baldufal/hpctl_avr/HPCtl/twislave.c

/*
* twislave.c
*
* Created: 23-Dec-22
* Author : Falk
* Source: https://rn-wissen.de/wiki/index.php/TWI_Slave_mit_avr-gcc
*
* We support all three types of I2C transactions:
* - Pure write: One byte can be written to address 0x0 to 0x3
* - Pure read: 6 bytes can be read, starting from address 0x0
* - Write+read: This is actually just a read from some given address (the one byte written).
*/

#include <util/twi.h>
#include <avr/interrupt.h>
#include <stdint.h>
#include "twislave.h"

// The currently selected register address (within i2cdata) to be read from/written to.
volatile uint8_t buffer_addr;

void init_twi_slave(uint8_t addr) {
	// I2C addresses are 7 bits! We have to shift.
	TWAR = (addr << 1);
	TWCR &= ~((1 << TWSTA) | (1 << TWSTO));
	TWCR |= (1 << TWEA) | (1 << TWEN) | (1 << TWIE);
	buffer_addr = 0xFF;
}

// Macros for TWI control register bitmasks

// ACK nach empfangenen Daten senden/ ACK nach gesendeten Daten erwarten
#define TWCR_ACK TWCR = (1<<TWEN)|(1<<TWIE)|(1<<TWINT)|(1<<TWEA)|(0<<TWSTA)|(0<<TWSTO)|(0<<TWWC);

// NACK nach empfangenen Daten senden/ NACK nach gesendeten Daten erwarten
#define TWCR_NACK TWCR = (1<<TWEN)|(1<<TWIE)|(1<<TWINT)|(0<<TWEA)|(0<<TWSTA)|(0<<TWSTO)|(0<<TWWC);

// Switch to the non-addressed slave mode...
#define TWCR_RESET TWCR = (1<<TWEN)|(1<<TWIE)|(1<<TWINT)|(1<<TWEA)|(0<<TWSTA)|(1<<TWSTO)|(0<<TWWC); buffer_addr=0xFF;

// TWI interrupt service routine
ISR (TWI_vect) {
	uint8_t data = 0;

	// Check TWI status register
	switch (TW_STATUS) {
		/*
		* Slave Receiver
		*/

		// 0x60 SLA+W received, ACK returned
		case TW_SR_SLA_ACK:
		// Receive next byte of data, send ACK afterwards
		TWCR_ACK;
		// Set "register address" to undefined
		buffer_addr = 0xFF;
		break;

		// 0x80 data received, ACK returned
		case TW_SR_DATA_ACK:
		// Read received data
		data = TWDR;

		// First access of this transaction, set register address
		if (buffer_addr == 0xFF) {
			// First byte of this transaction
			// This specifies the register address, usually.
			if (data < i2c_buffer_size) {
				buffer_addr = data;
			}

			// Receive next byte, ACK afterwards to request next byte
			TWCR_ACK;
			} else {
			// Subsequent byte(s) of this transaction
			// We can now receive data and use it.

			// Check which address we write to
			switch(buffer_addr) {
				// Temporary inconsistency of status register is fine because interrupts are disabled.
				
				case 0:
				// Heater Level
				if(data <= 30)
				i2cdata[buffer_addr] = data;
				break;
				
				case 1:
				// Vent IN
				if(data <= 6)
				i2cdata[buffer_addr] = data;
				break;
				
				case 2:
				// Vent OUT
				i2cdata[buffer_addr] = data;
				break;
				
				case 3:
				// SSRs
				
				// Some bits are write protected because they are set by heater level and ventilator PWM.
				i2cdata[buffer_addr] &= 0b11101000;
				i2cdata[buffer_addr] |= (data & 0b00010111);
				break;
				
				// Ignore writes to other addresses
			}

			// Increase address for subsequent writes
			buffer_addr++;

			// Receive next byte, ACK afterwards to request next byte
			TWCR_ACK;
		}
		break;

		// 0xA0 stop or repeated start condition received while selected
		case TW_SR_STOP:
		TWCR_ACK;
		break;

		/*
		* Slave Transmitter
		*/

		//0xA8 SLA+R received, ACK returned
		case TW_ST_SLA_ACK:
		// fall through

		// 0xB8 data transmitted, ACK received
		case TW_ST_DATA_ACK:
		if (buffer_addr >= i2c_buffer_size) {
			// This is either a pure read transaction (no Write+Read, buffer_addr=0xFF set via previous TWCR_RESET)
			// or something else went wrong.
			// We'll just assume they want to read everything...
			buffer_addr = 0x00;
		}

		if (buffer_addr < i2c_buffer_size) {
			// Send one byte of data
			TWDR = i2cdata[buffer_addr];

			if (buffer_addr == (i2c_buffer_size - 1)) {
				// Indicate that this is the last byte available, i.e. expect a NACK after we transmitted it.
				TWCR_NACK
				break;
			}

			// Auto increment address
			buffer_addr++;
			} else {
			// Invalid address/read too many bytes/... -- we send 0xFE as an error
			TWDR = 0xFE;
		}
		TWCR_ACK;
		break;

		/*
		* Error states
		*/
		case TW_ST_DATA_NACK: // 0xC0 data transmitted, NACK received. No further data requested.
		case TW_SR_DATA_NACK: // 0x88 data received, NACK returned
		case TW_ST_LAST_DATA: // 0xC8 last data byte (TWEA=0) transmitted, ACK received
		default:
		TWCR_RESET;
		break;
	}
}
