baldufal/hpctl_avr/HPCtl/twislave.h

/*
 * twislave.h
 *
* Created: 05-Oct-23
* Author : Falk
 * Source: https://rn-wissen.de/wiki/index.php/TWI_Slave_mit_avr-gcc
 */

#ifndef TWISLAVE_H_
#define TWISLAVE_H_

#include <util/twi.h>
#include <avr/interrupt.h>
#include <stdint.h>

// I2C data buffer size.
// [0]: Heater Level (determines SSR5 to SSR7) (r/w)
// [1]: Ventilation IN (r/w)
// [2]: Ventilation OUT (r/w) (determines SSR3)
// [3]: SSR0 to SSR2 & SSR4 values (r/w)
// [4]: checksum byte (r)
// [5]: Input values and complement (r/w)
//
#define i2c_buffer_size 6

// I2C slave address.
#define I2C_SLAVE_ADDRESS 0x3f

// Status register flags.
#define I2C_BIT_READOUT 0x01
#define I2C_BIT_WDT_RESET 0x02

volatile uint8_t i2cdata[i2c_buffer_size];

// Initializes TWI with the given address.
// I2C addresses are 7 bytes, init_twi_slave will shift the given address by one bit.
void init_twi_slave(uint8_t addr);

// Don't change below here

// Old versions of AVR-GCC do interrupt stuff differently.
#if (__GNUC__ * 100 + __GNUC_MINOR__) < 304
#error "This library requires AVR-GCC 3.4.5 or later, update to newer AVR-GCC compiler"
#endif

#if (i2c_buffer_size > 254)
#error buffer size needs to be less than 254.
#endif

#if (i2c_buffer_size < 2)
#error buffer size needs to be at least two bytes.
#endif

#endif /* TWISLAVE_H_ */
